xa7medx69-oss/game/assets/expansion-pack/game-01.png

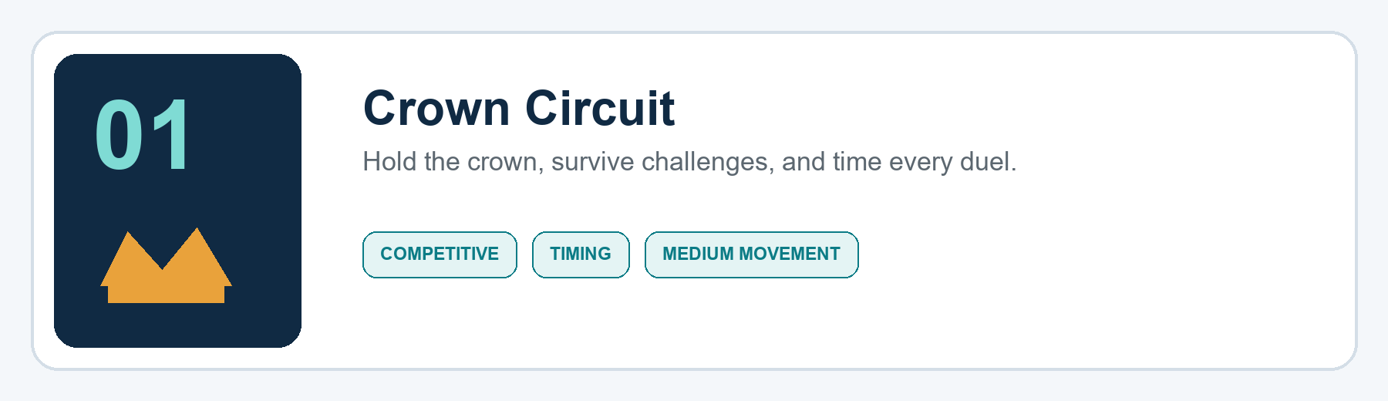
assets/expansion-pack/game-01.png
