xa7medx69-oss/game/assets/expansion-pack/game-02.png

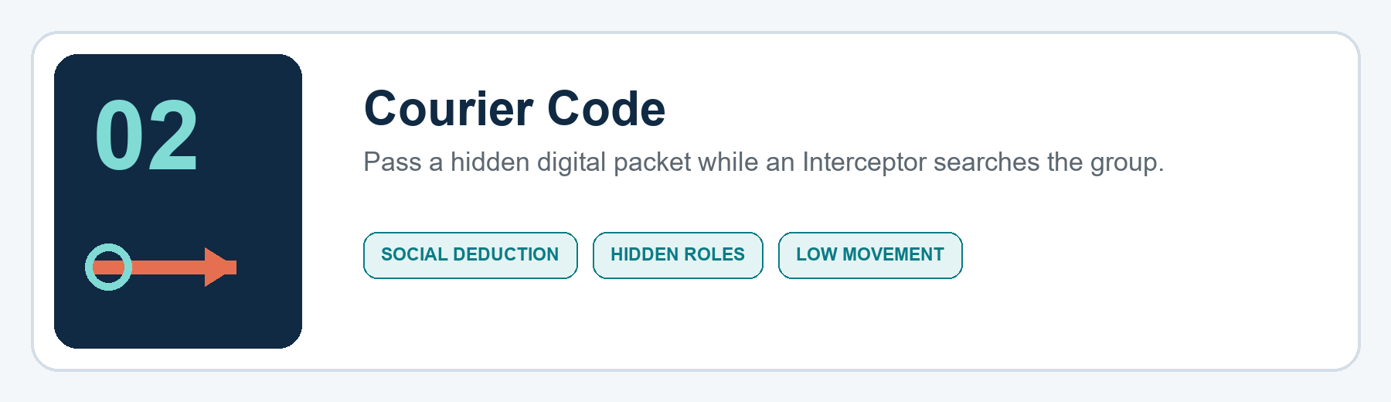
assets/expansion-pack/game-02.png
