xa7medx69-oss/game/assets/expansion-pack/game-04.png

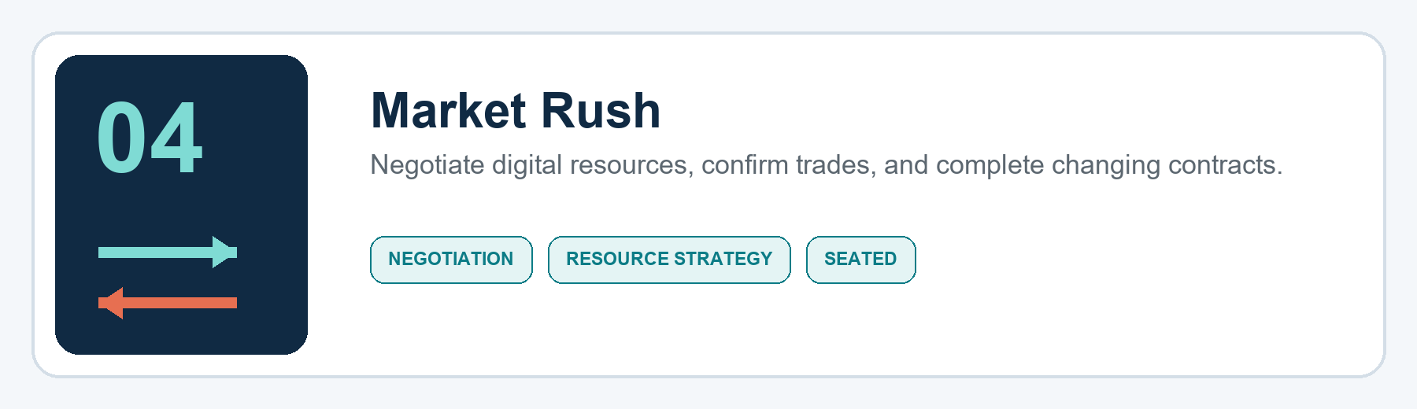
assets/expansion-pack/game-04.png
