xa7medx69-oss/game/assets/expansion-pack/game-06.png

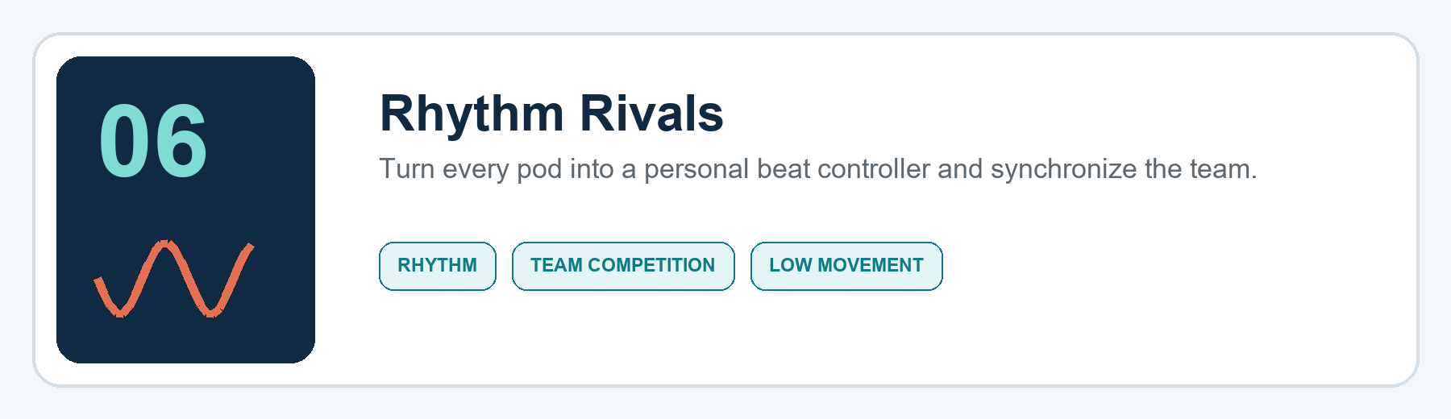
assets/expansion-pack/game-06.png
