xa7medx69-oss/game/assets/expansion-pack/library-map.png

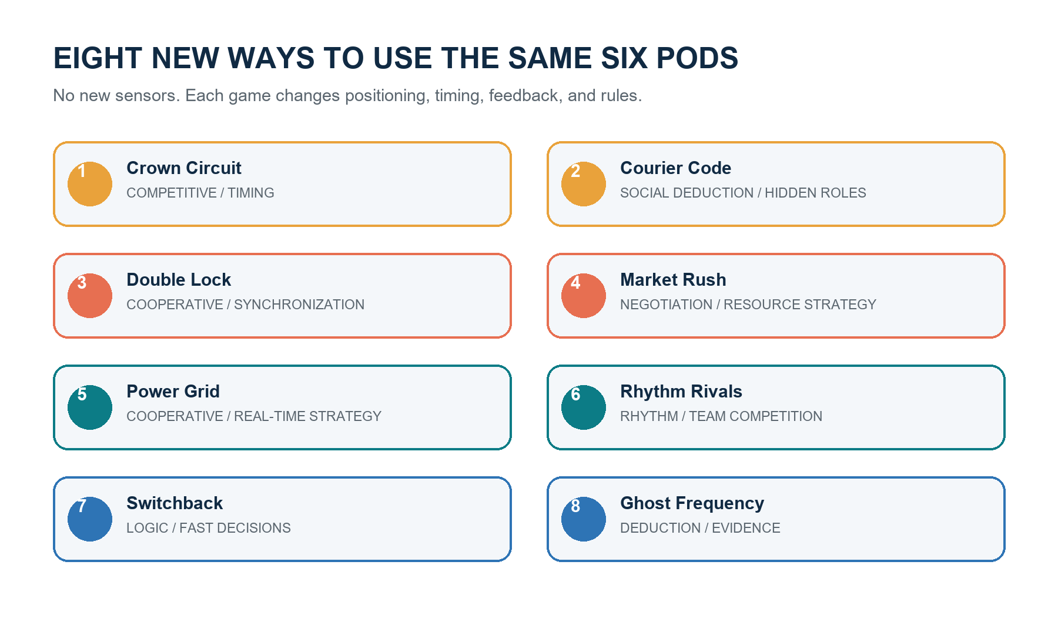
assets/expansion-pack/library-map.png
