xa7medx69-oss/game/assets/games/01-pulse-hunt.png

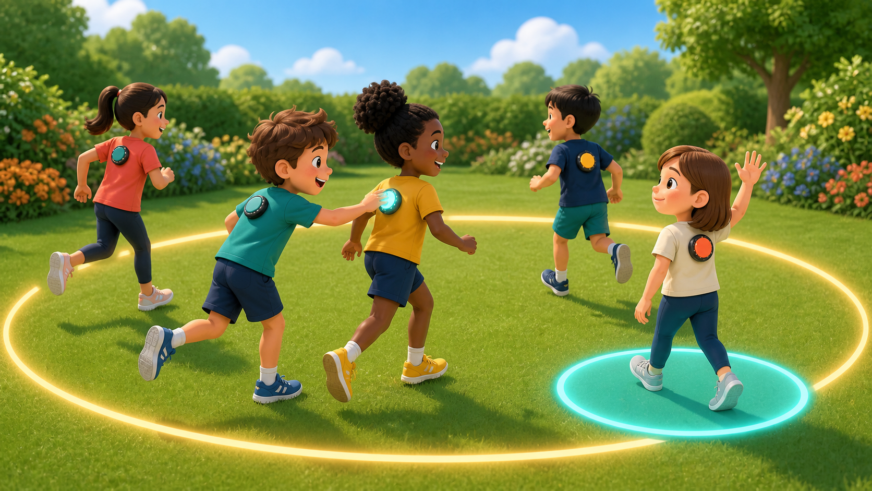
assets/games/01-pulse-hunt.png
