xa7medx69-oss/game/assets/games/03-signal-chain.png

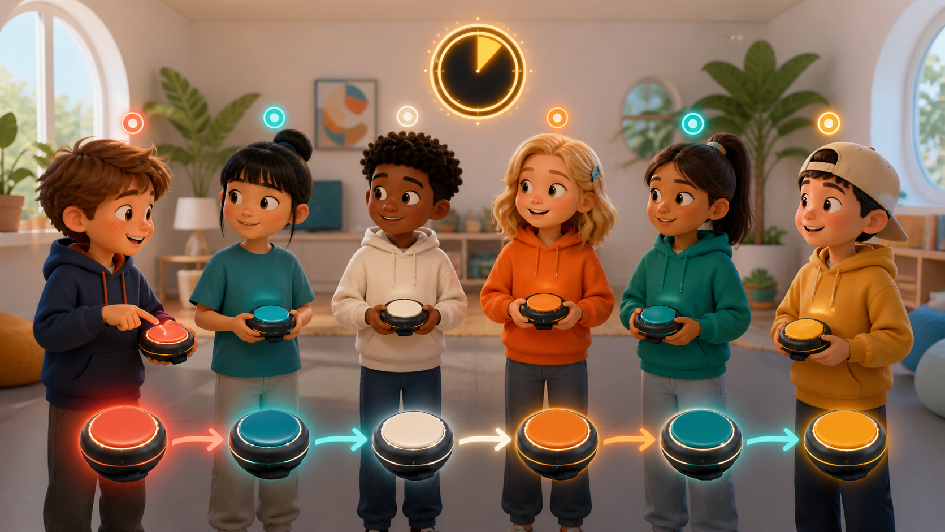
assets/games/03-signal-chain.png
