xa7medx69-oss/game/assets/games/04-guardian-link.png

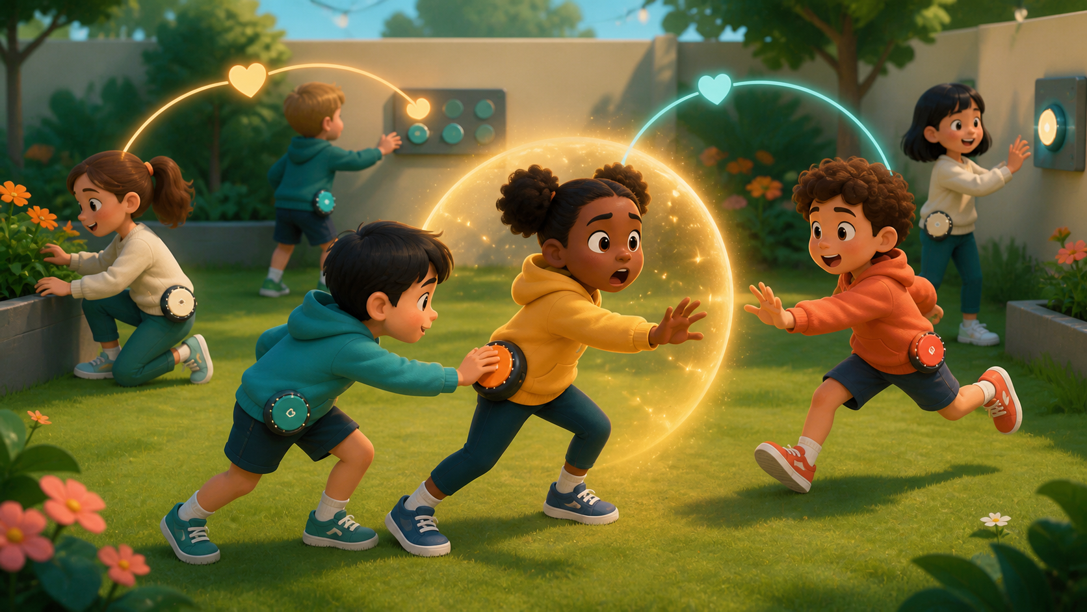
assets/games/04-guardian-link.png
