xa7medx69-oss/game/assets/games/05-territory-pulse.png

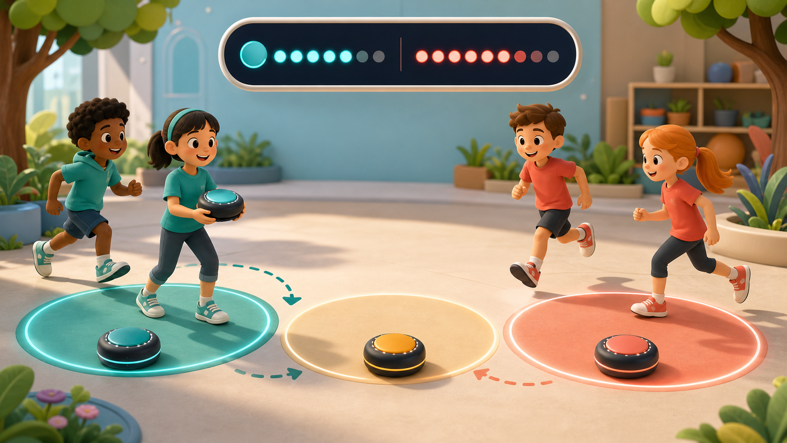
assets/games/05-territory-pulse.png
