xa7medx69-oss/game/assets/games/06-echo-match.png

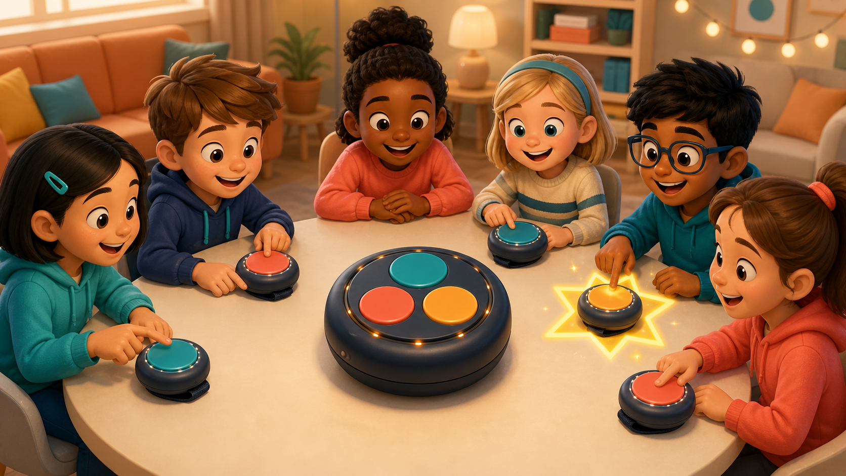
assets/games/06-echo-match.png
