xa7medx69-oss/game/assets/games/07-silent-mission.png

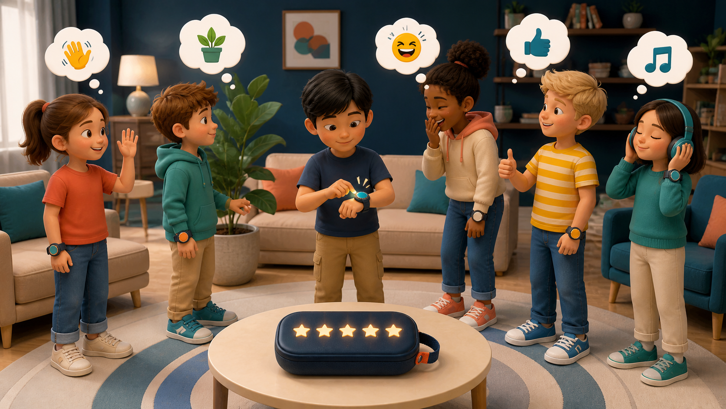
assets/games/07-silent-mission.png
