xa7medx69-oss/game/assets/games/08-relay-rush.png

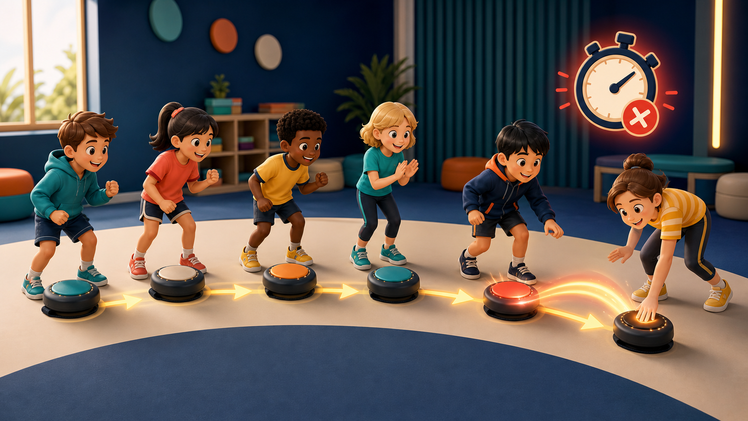
assets/games/08-relay-rush.png
