xa7medx69-oss/game/assets/games/09-crown-circuit.png

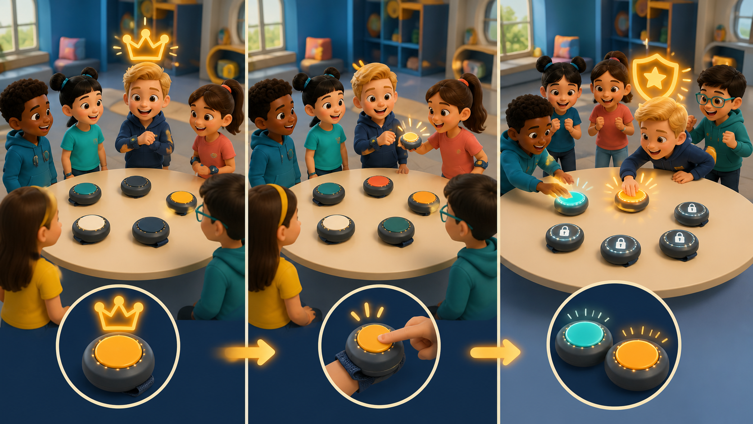
assets/games/09-crown-circuit.png
