xa7medx69-oss/game/assets/games/10-courier-code.png

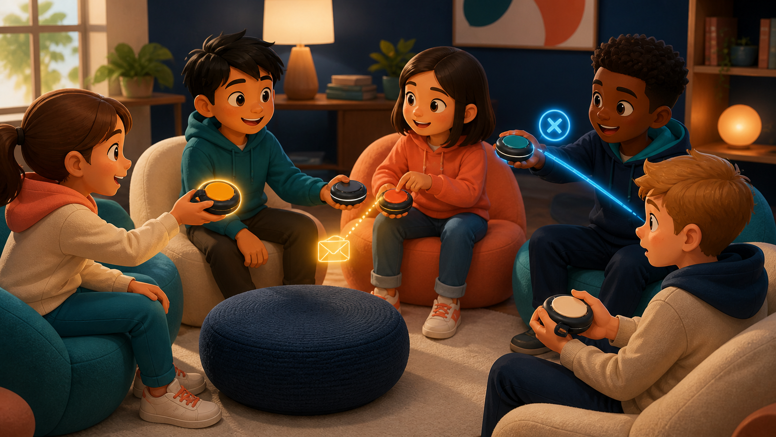
assets/games/10-courier-code.png
