xa7medx69-oss/game/assets/games/11-double-lock.png

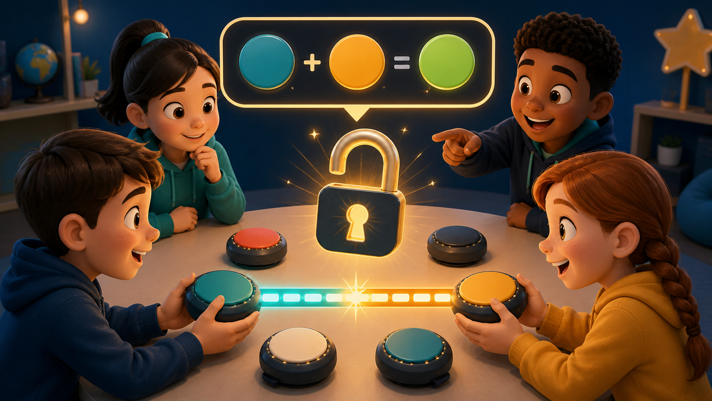
assets/games/11-double-lock.png
