xa7medx69-oss/game/assets/games/13-power-grid.png

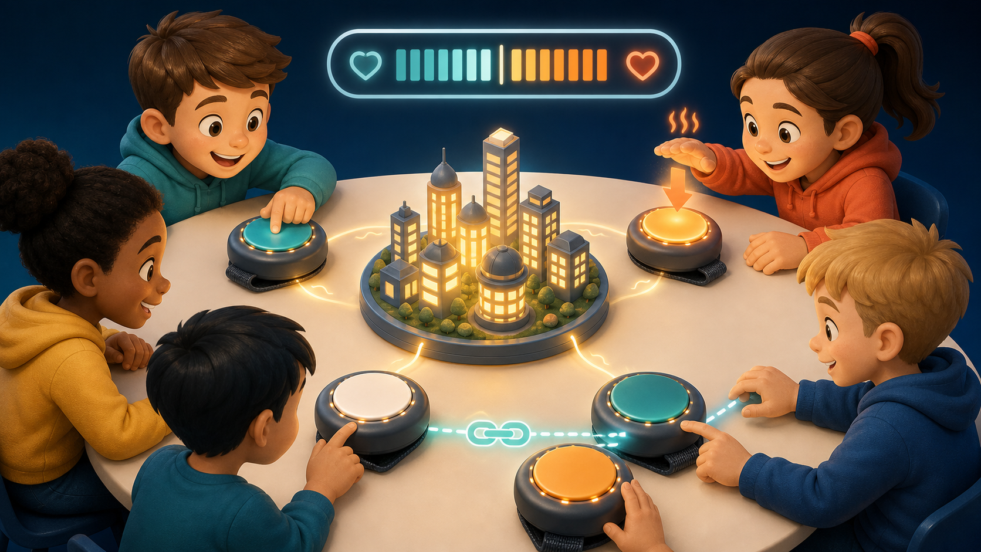
assets/games/13-power-grid.png
