xa7medx69-oss/game/assets/games/14-rhythm-rivals.png

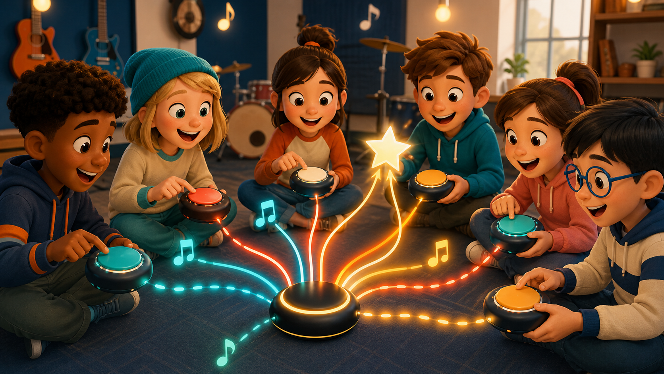
assets/games/14-rhythm-rivals.png
