xa7medx69-oss/game/assets/games/15-switchback.png

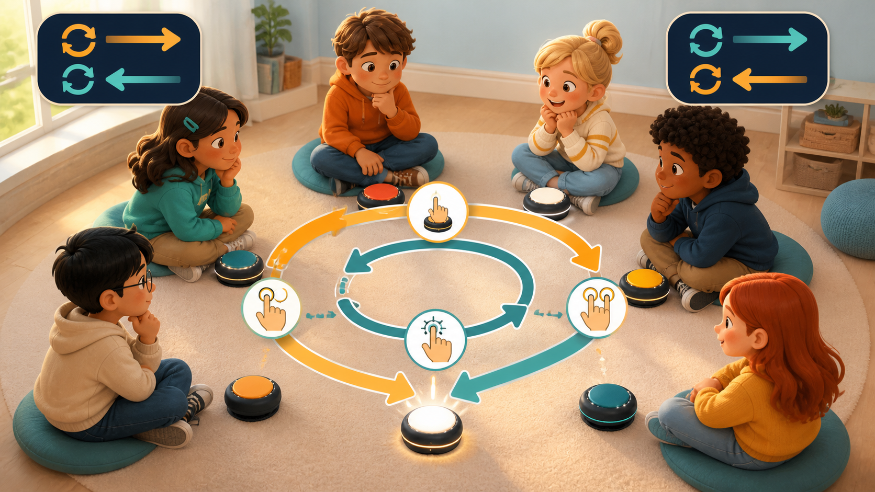
assets/games/15-switchback.png
