xa7medx69-oss/game/assets/games/16-ghost-frequency.png

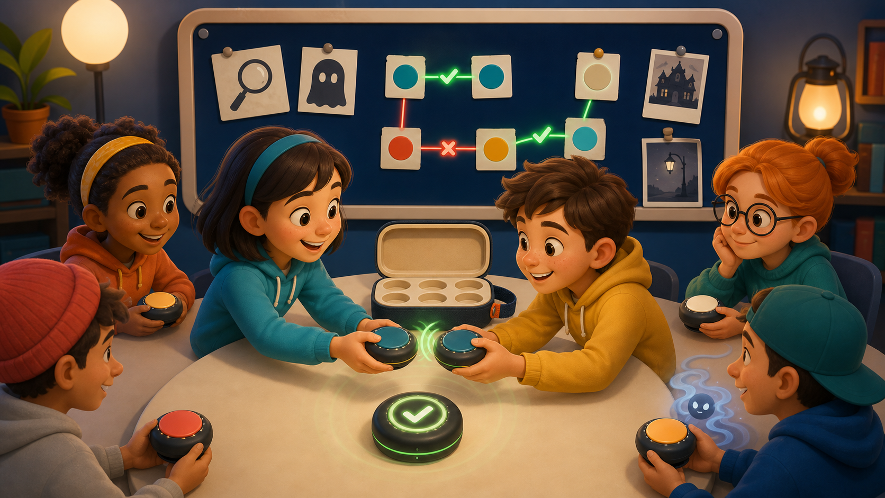
assets/games/16-ghost-frequency.png
