xa7medx69-oss/game/assets/handbook/gameplay-villa.png

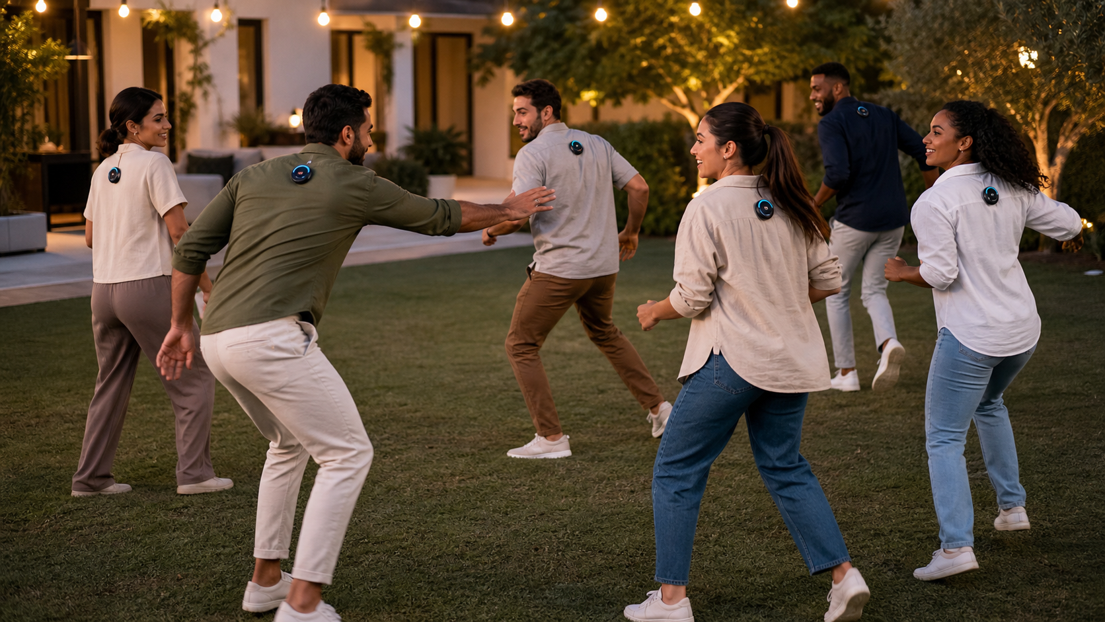
assets/handbook/gameplay-villa.png
