xa7medx69-oss/game/assets/handbook/node-blocks.png

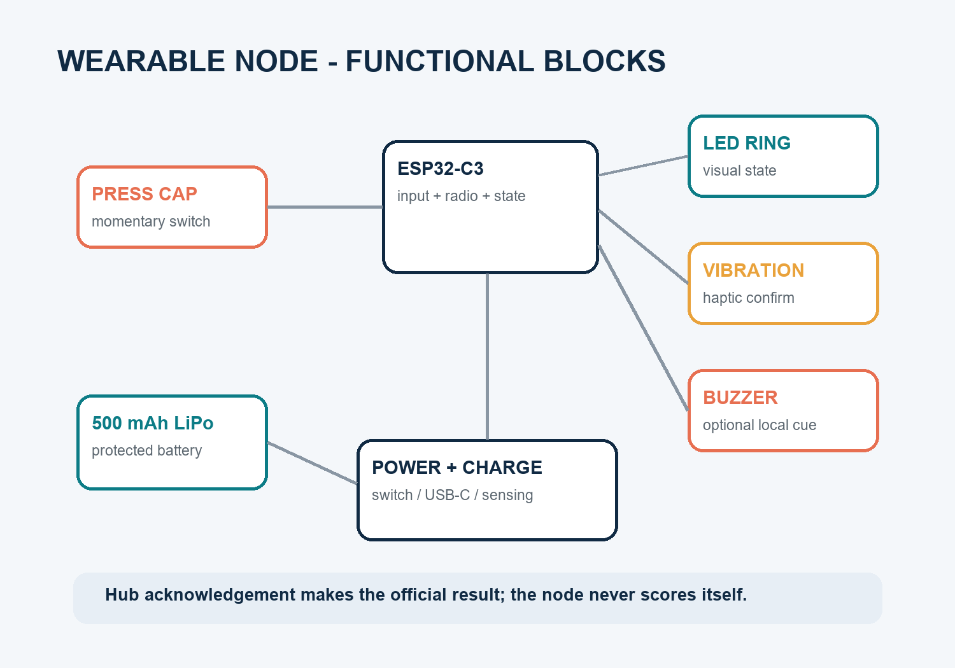
assets/handbook/node-blocks.png
