xa7medx69-oss/game/assets/handbook/wearable-exploded.png

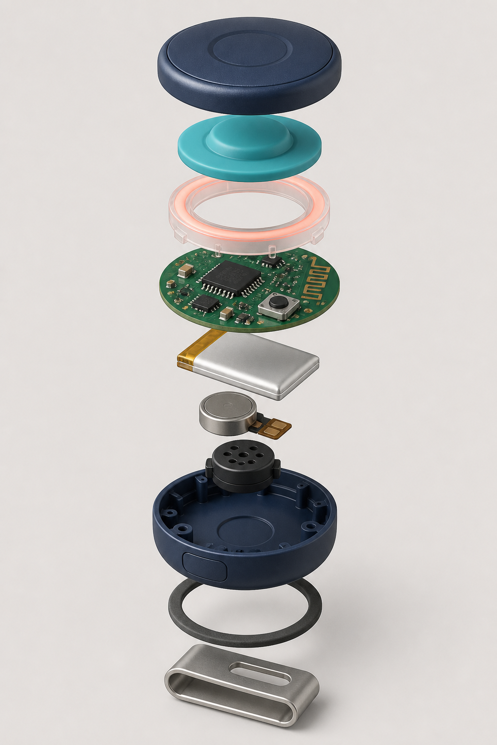
assets/handbook/wearable-exploded.png
