xa7medx69-oss/game/manuals/chapters/17-branding-manual.md

> Physical Social Games Business | Manual 17 | Version 0.1 | 2026-08-19

# Branding Manual

## Positioning
A modern physical play platform that makes gatherings active, surprising, and replayable. The brand is original and should never depend on a television programme, copied terminology, name-tag imagery, or recognizable show styling.

## Working brand criteria
Short in Arabic and English, easy to pronounce, broad enough for many game types, available as a UAE trademark/domain/social handle, and not descriptive of only chasing or buttons. Do not select a final name before clearance.

## Personality
Premium but welcoming; energetic without aggression; clever without being complicated; locally relevant without stereotypes. Use concise host language and celebratory feedback.

## Visual direction
Deep navy foundation, teal action color, coral highlight, amber reward, warm off-white background. Rounded geometry echoes the pod without making every graphic a button. Photography shows real groups and safe open spaces, not staged combat poses.

## Voice examples
Prefer: "Choose a game. Clip in. Start the round." "Six ready." "Signal confirmed." Avoid: militaristic language, copied show phrases, humiliation after elimination, and claims such as "unbreakable" or "works everywhere."

## Naming sprint
Generate 50 candidates; remove narrow/copycat names; screen search engines, domains, app stores, trade names, and trademarks; test pronunciation with Arabic/English speakers; shortlist five; obtain professional clearance; then design the identity.
