xa7medx69-oss/game/manuals/chapters/19-business-model-manual.md

> Physical Social Games Business | Manual 19 | Version 0.1 | 2026-08-19

# Business Model Manual

## Primary model
Sell a reusable hardware kit with an included permanent game library. Grow lifetime value through optional expansion pods, accessories, new premium games, gifting, events, and replacement/service—not by disabling core functionality behind a subscription.

## Customer segments
UAE families/friends; gift buyers; party/event organizers; hospitality venues; youth/community groups after safety validation; later corporate team-building providers and regional distributors.

## Channels
Direct online pre-orders, pop-up demonstrations, partnerships with event organizers, curated gift retailers, corporate pilots, and rentals. The product needs live demonstration because the value is experiential.

## Unit-economics worksheet
Revenue minus landed COGS, payment fees, fulfilment, warranty/returns, customer support, and variable content/service cost equals contribution margin. Compare contribution margin against blended customer acquisition cost and return/refund rate.

## Defensibility
Reliable hardware/software integration, original tested game library, brand/community, proprietary event/game engine, industrial design, manufacturing know-how, and accumulated anonymous playtest insights. Game ideas alone are weak protection.
