xa7medx69-oss/game/manuals/chapters/20-marketing-manual.md

> Physical Social Games Business | Manual 20 | Version 0.1 | 2026-08-19

# Marketing Manual

## Core message
One compact kit changes what a gathering can become: active games, team challenges, reaction rounds, and low-mobility social missions using the same six devices.

## Proof content
Show setup in under five minutes; a clear 15-second gameplay loop; real reactions; multiple distinct games; offline play; safe play-space setup; kit reset and replay. Avoid implying association with any television show.

## Launch content plan
Founder build story; product reveal; how-it-works animation; three game demos; host tutorial; UAE villa/ghabga use case; reliability test; playtester reactions; pricing/pre-order; delivery/support updates.

## Demonstration funnel
Short video -> landing page -> email/waitlist -> small paid or deposit-backed playtest -> pre-order. Measure click-through, qualified signup, demo attendance, deposit conversion, acquisition cost, and refund intent.

## Community loop
Invite owners to vote on new mechanics, publish seasonal game updates, run host challenges, and reward useful playtest reports. Moderate for safety and never collect children's content without a dedicated compliant process.
