xa7medx69-oss/game/manuals/chapters/23-legal-and-ip-manual.md

> Physical Social Games Business | Manual 23 | Version 0.1 | 2026-08-19

# Legal and IP Manual

## Originality boundary
Do not use the Running Man name, logos, visual identity, character/personality references, episode formats, signature props, promotional comparisons suggesting affiliation, or copied game presentations. Document independent development of names, rules, artwork, hardware, UI, and marketing.

## Protection stack
Trademark for final brand/product names and logos; copyright for software, artwork, manuals, sound, and written game expression; industrial design for distinctive product appearance; patent/utility analysis for genuinely novel technical inventions; contracts and confidentiality for supplier/source assets and unreleased designs.

UAE's Ministry of Economy and Tourism is the competent authority for trademarks, copyright registrations, patents, and industrial property. UAE guidance also notes that schemes, rules, or methods for playing games are not granted patents as such, while qualifying technical inventions may be evaluated separately: https://u.ae/en/information-and-services/business/intellectual-property

## Before naming or launch
Conduct UAE and relevant international trademark clearance; search company/trade names, domains, app stores, marketplaces, and social handles; document results; obtain professional advice on Nice classes likely covering games/toys, electronics, software, retail, and entertainment services.

## Contracts
Founder IP assignment; contractor work-made/assignment and confidentiality; firmware/software licences and open-source notices; manufacturer NDA, tooling ownership, quality/change controls, and no unauthorized production; playtester consent/release; retailer/distributor terms; privacy/website terms; warranty/returns.

## Claims discipline
Substantiate range, battery life, water resistance, age suitability, safety, durability, and number of included games. Do not claim certification before approval or use "patented" unless accurate for the jurisdiction/status.
